geaz/simplyKeeb-60K/printedmx/keeb/positions.scad

withTrrs = true;

// [x, y]
screwPositions = [
    [5.2,-105.5],
    [22.6,-79.9],
    [60.7,-79.9],
    [98.8,-79.9],
    [98.8,-22.3],  
    [22.6,-22.3],  
    [60.7,-41.5]
];

bendPreventions = [
    [61, -22.3],
    [32, -41.5],
    [89, -41.5],
    [32, -60.5],
    [89, -60.5],
    [61, -79.9],
];

// x, y, rotation
proMicroPosition = [40,-36.2,0];
trrsPosition = [-12,-95.7,15];
