geaz/simplyKeeb-60K/pcb/RP2040_for_keebs.kicad_sch

## KiCad design pcb/RP2040_for_keebs.kicad_sch (2022-11-28)

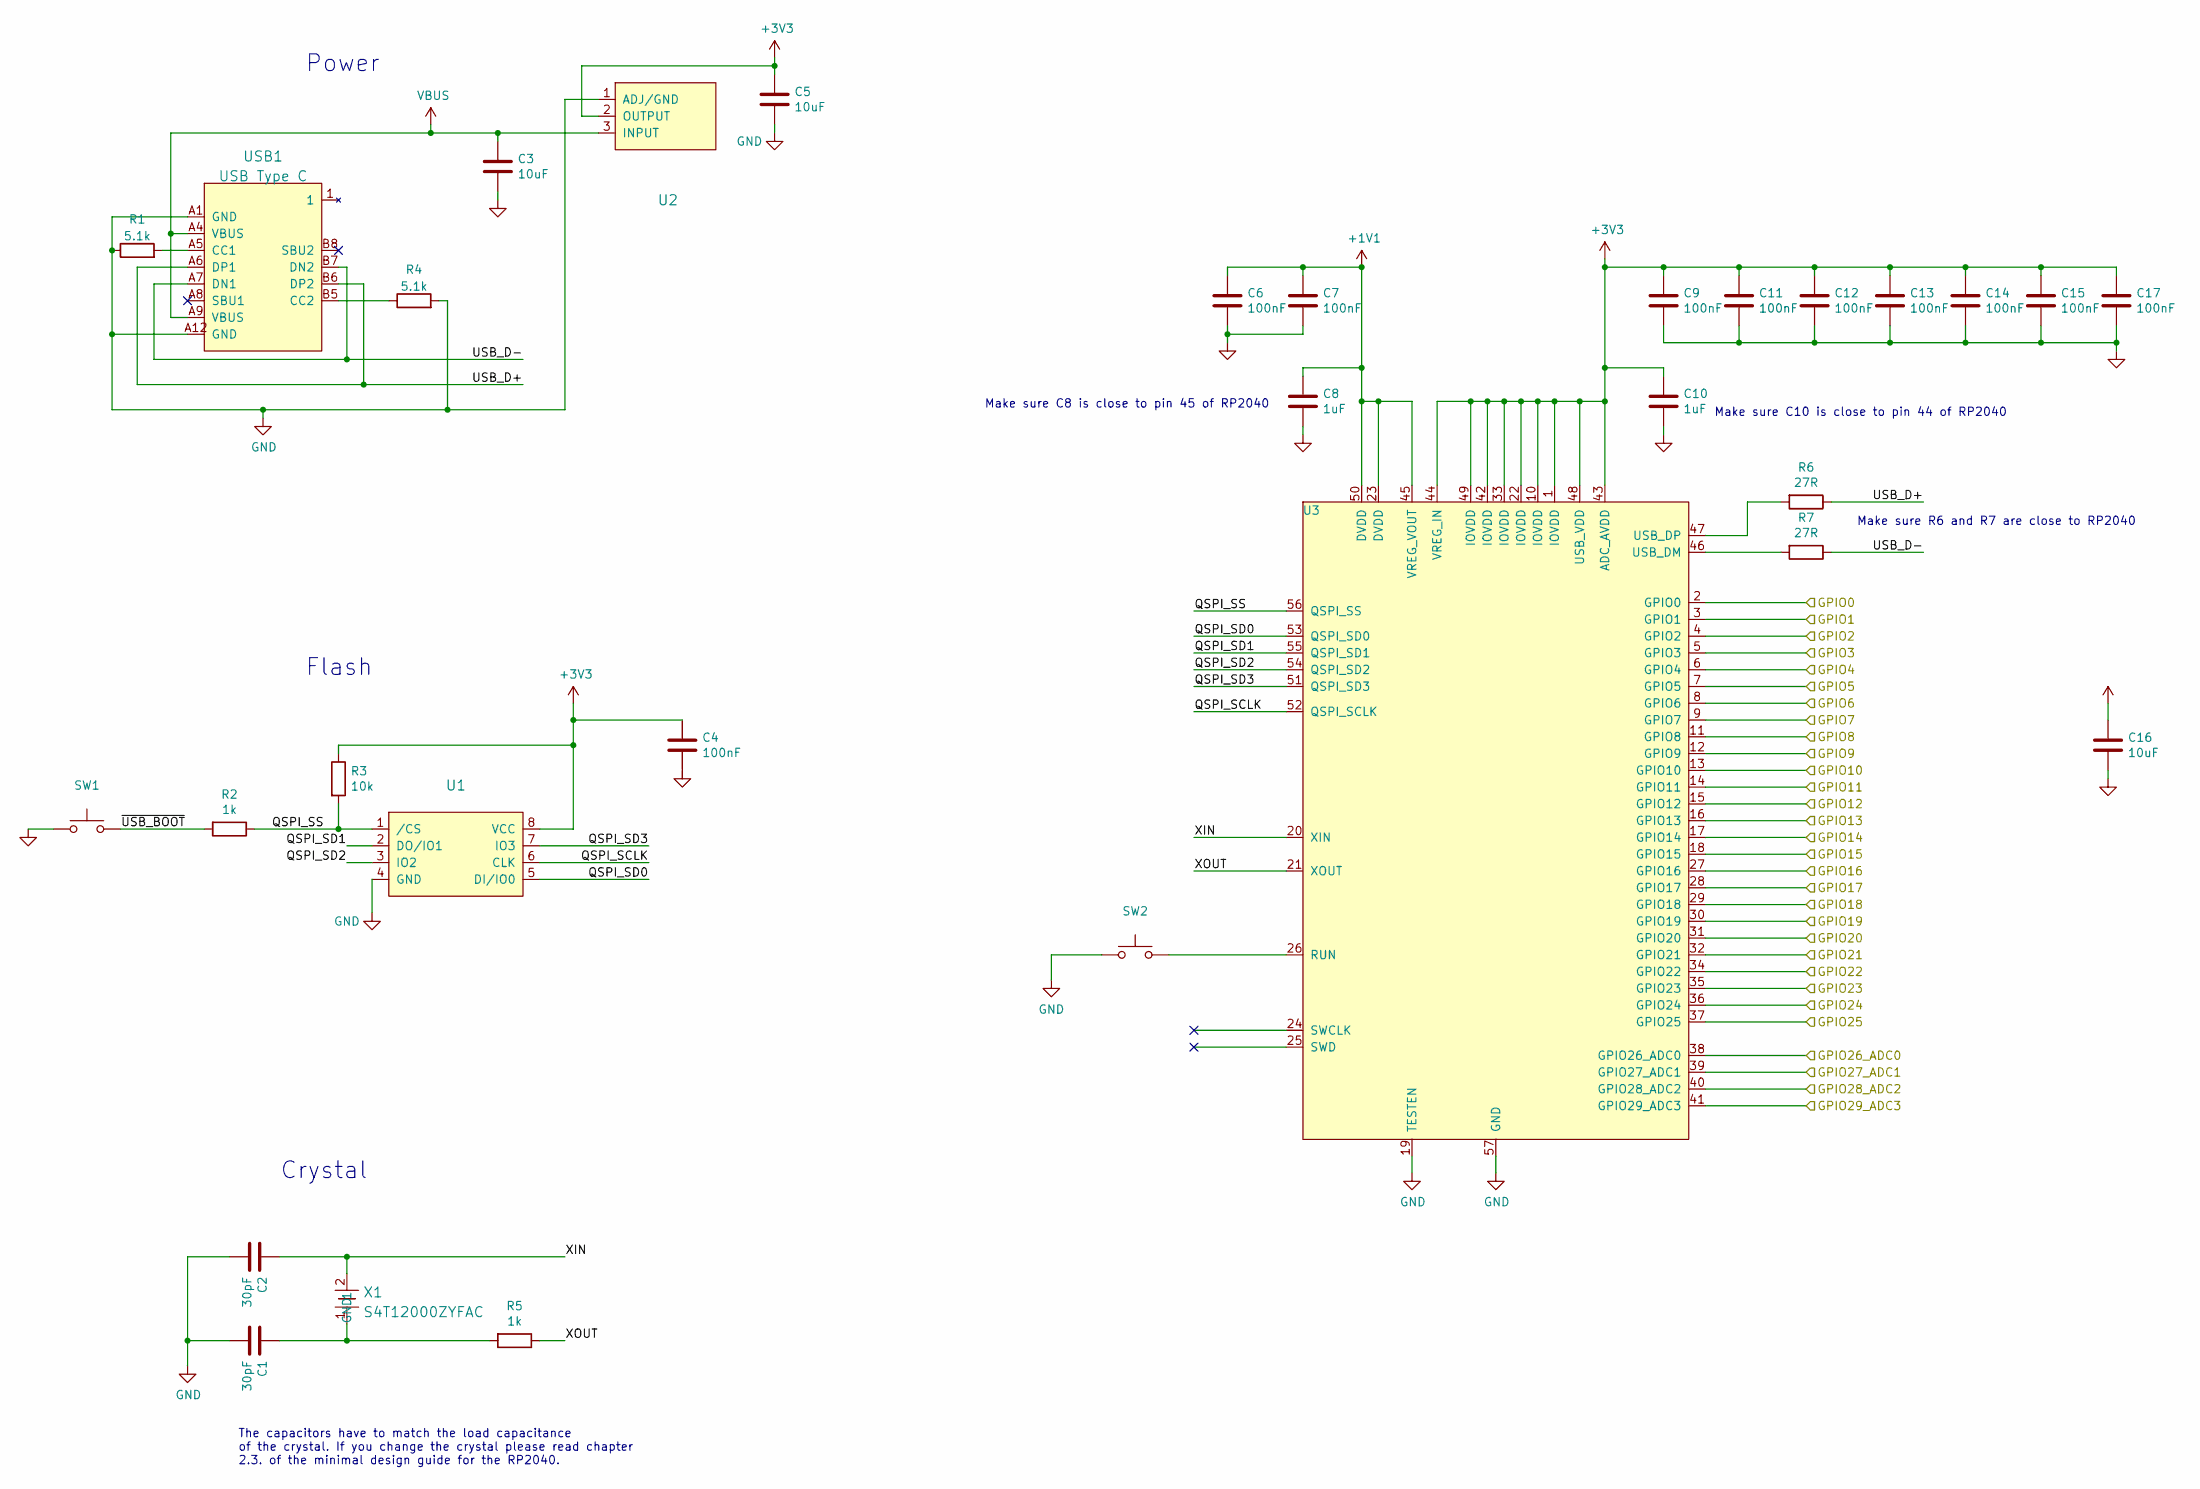
[picture p35: schematic RP2040_for_keebs.kicad_sch]

Parts:
C1, C2: 30pF; C_0402_1005Metric
C3, C5, C16: 10uF; C_0402_1005Metric
C4: 100nF; C_0402_1005Metric
C6, C7, C9, C11, C12, C13, C14, C15, C17: 100nF; C_0402_1005Metric; LCSC C83056
C8, C10: 1uF; C_0402_1005Metric; LCSC C92755
R1, R4: 5.1k; R_0402_1005Metric
R2, R5: 1k; R_0402_1005Metric
R3: 10k; R_0402_1005Metric
R6, R7: 27R; R_0402_1005Metric; LCSC C25100
SW1, SW2: SW-SMD_L6.0-W3.3-LS8.0
U1: SOIC-8_L5.3-W5.3-P1.27-LS8.0-BL; LCSC C82317
U2: SOT-223-3_L6.5-W3.4-P2.30-LS7.0-BR; LCSC C26537
U3: RP2040; LCSC C2040
USB1: USB Type C; USB-C-SMD_TYPE-C-31-M-31; LCSC C2760486
X1: S4T12000ZYFAC; CRYSTAL-SMD_L7.4-W4.0-LS8.0; LCSC C2149004

Connections:
+1V1: C6.1, C7.1, C8.1, U3.23 (DVDD), U3.45 (VREG_VOUT), U3.50 (DVDD)
+3V3: C4.1, C5.1, C9.1, C10.1, C11.1, C12.1, C13.1, C14.1, C15.1, C17.1, R3.1, U1.8 (VCC), U2.2 (OUTPUT), U3.1 (IOVDD), U3.10 (IOVDD), U3.22 (IOVDD), U3.33 (IOVDD), U3.42 (IOVDD), U3.43 (ADC_AVDD), U3.44 (VREG_IN), U3.48 (USB_VDD), U3.49 (IOVDD)
GND: C1.2, C2.2, C5.2, R1.1, R4.2, SW2.1, U1.4 (GND), U2.1 (ADJ/GND), U3.19 (TESTEN), U3.57 (GND), USB1.A1 (GND), USB1.A12 (GND)
GPIO0: U3.2 (GPIO0)
GPIO1: U3.3 (GPIO1)
GPIO2: U3.4 (GPIO2)
GPIO3: U3.5 (GPIO3)
GPIO4: U3.6 (GPIO4)
GPIO5: U3.7 (GPIO5)
GPIO6: U3.8 (GPIO6)
GPIO7: U3.9 (GPIO7)
GPIO8: U3.11 (GPIO8)
GPIO9: U3.12 (GPIO9)
GPIO10: U3.13 (GPIO10)
GPIO11: U3.14 (GPIO11)
GPIO12: U3.15 (GPIO12)
GPIO13: U3.16 (GPIO13)
GPIO14: U3.17 (GPIO14)
GPIO15: U3.18 (GPIO15)
GPIO16: U3.27 (GPIO16)
GPIO17: U3.28 (GPIO17)
GPIO18: U3.29 (GPIO18)
GPIO19: U3.30 (GPIO19)
GPIO20: U3.31 (GPIO20)
GPIO21: U3.32 (GPIO21)
GPIO22: U3.34 (GPIO22)
GPIO23: U3.35 (GPIO23)
GPIO24: U3.36 (GPIO24)
GPIO25: U3.37 (GPIO25)
GPIO26_ADC0: U3.38 (GPIO26_ADC0)
GPIO27_ADC1: U3.39 (GPIO27_ADC1)
GPIO28_ADC2: U3.40 (GPIO28_ADC2)
GPIO29_ADC3: U3.41 (GPIO29_ADC3)
unnamed: C1.1, R5.2, X1.1
unnamed: R1.2, USB1.A5 (CC1)
unnamed: R4.1, USB1.B5 (CC2)
unnamed: R6.2, U3.47 (USB_DP)
unnamed: R7.2, U3.46 (USB_DM)
unnamed: SW2.2, U3.26 (RUN)
QSPI_SCLK: U1.6 (CLK), U3.52 (QSPI_SCLK)
QSPI_SD0: U1.5 (DI/IO0), U3.53 (QSPI_SD0)
QSPI_SD1: U1.2 (DO/IO1), U3.55 (QSPI_SD1)
QSPI_SD2: U1.3 (IO2), U3.54 (QSPI_SD2)
QSPI_SD3: U1.7 (IO3), U3.51 (QSPI_SD3)
QSPI_SS: R2.1, R3.2, U1.1 (/CS), U3.56 (QSPI_SS)
USB_D+: R6.1, USB1.A6 (DP1), USB1.B6 (DP2)
USB_D-: R7.1, USB1.A7 (DN1), USB1.B7 (DN2)
VBUS: C3.1, U2.3 (INPUT), USB1.A4 (VBUS), USB1.A9 (VBUS)
XIN: C2.1, U3.20 (XIN), X1.2 (GND)
XOUT: R5.1, U3.21 (XOUT)
~: C3.2, C4.2, C6.2, C7.2, C8.2, C9.2, C10.2, C11.2, C12.2, C13.2, C14.2, C15.2, C16.1, C16.2, C17.2, SW1.1
~USB_BOOT: R2.2, SW1.2

Notes on the sheet:
Make sure C10 is close to pin 44 of RP2040
The capacitors have to match the load capacitance of the crystal. If you change the crystal please read chapter 2.3. of the minimal design guide for the RP2040.
Power
Crystal
Make sure C8 is close to pin 45 of RP2040
Flash
Make sure R6 and R7 are close to RP2040
