geaz/simplyKeeb-60K/pcb/simplyKeeb-60K.kicad_sch

## KiCad design pcb/simplyKeeb-60K.kicad_sch (2022-11-28)

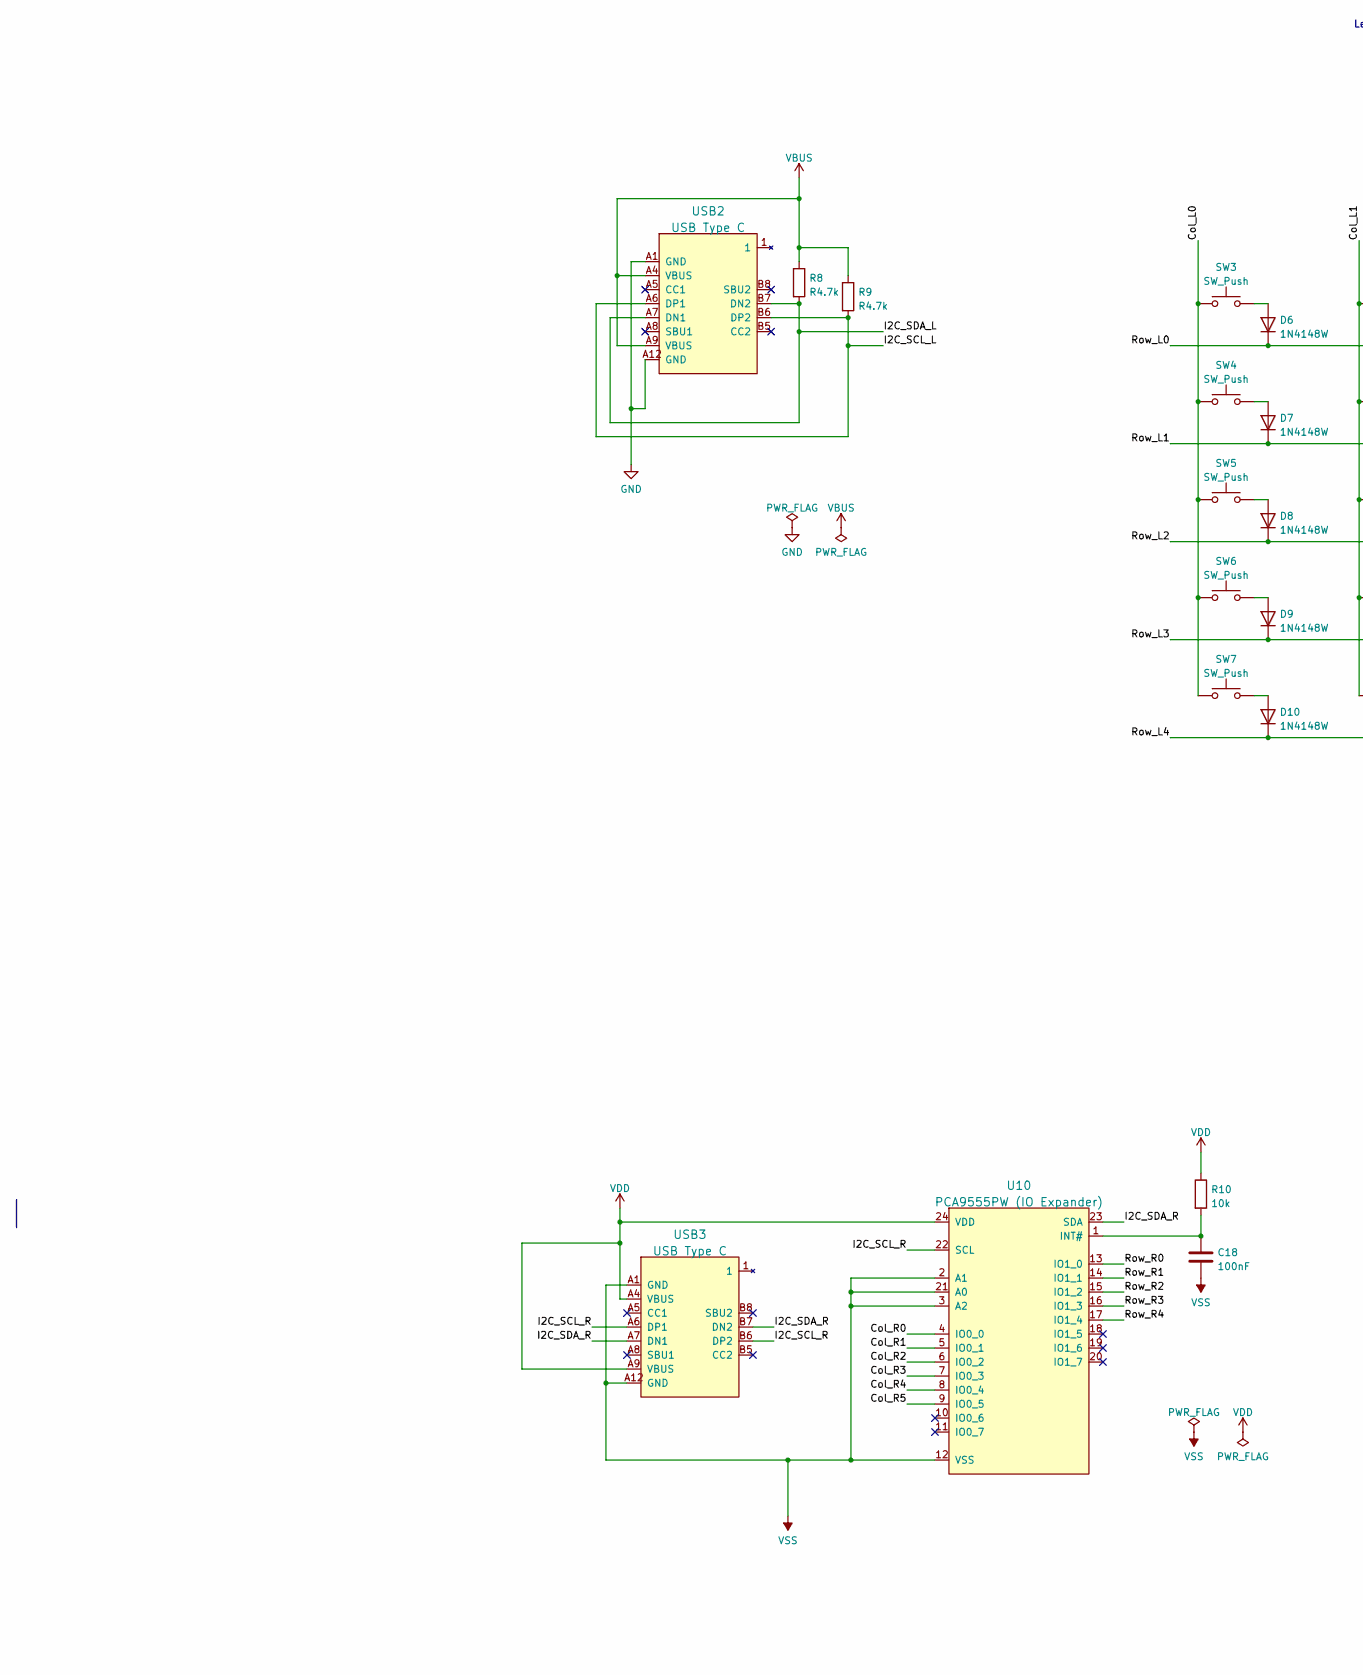
[picture p36: schematic simplyKeeb-60K.kicad_sch, part in row 1, column 1]

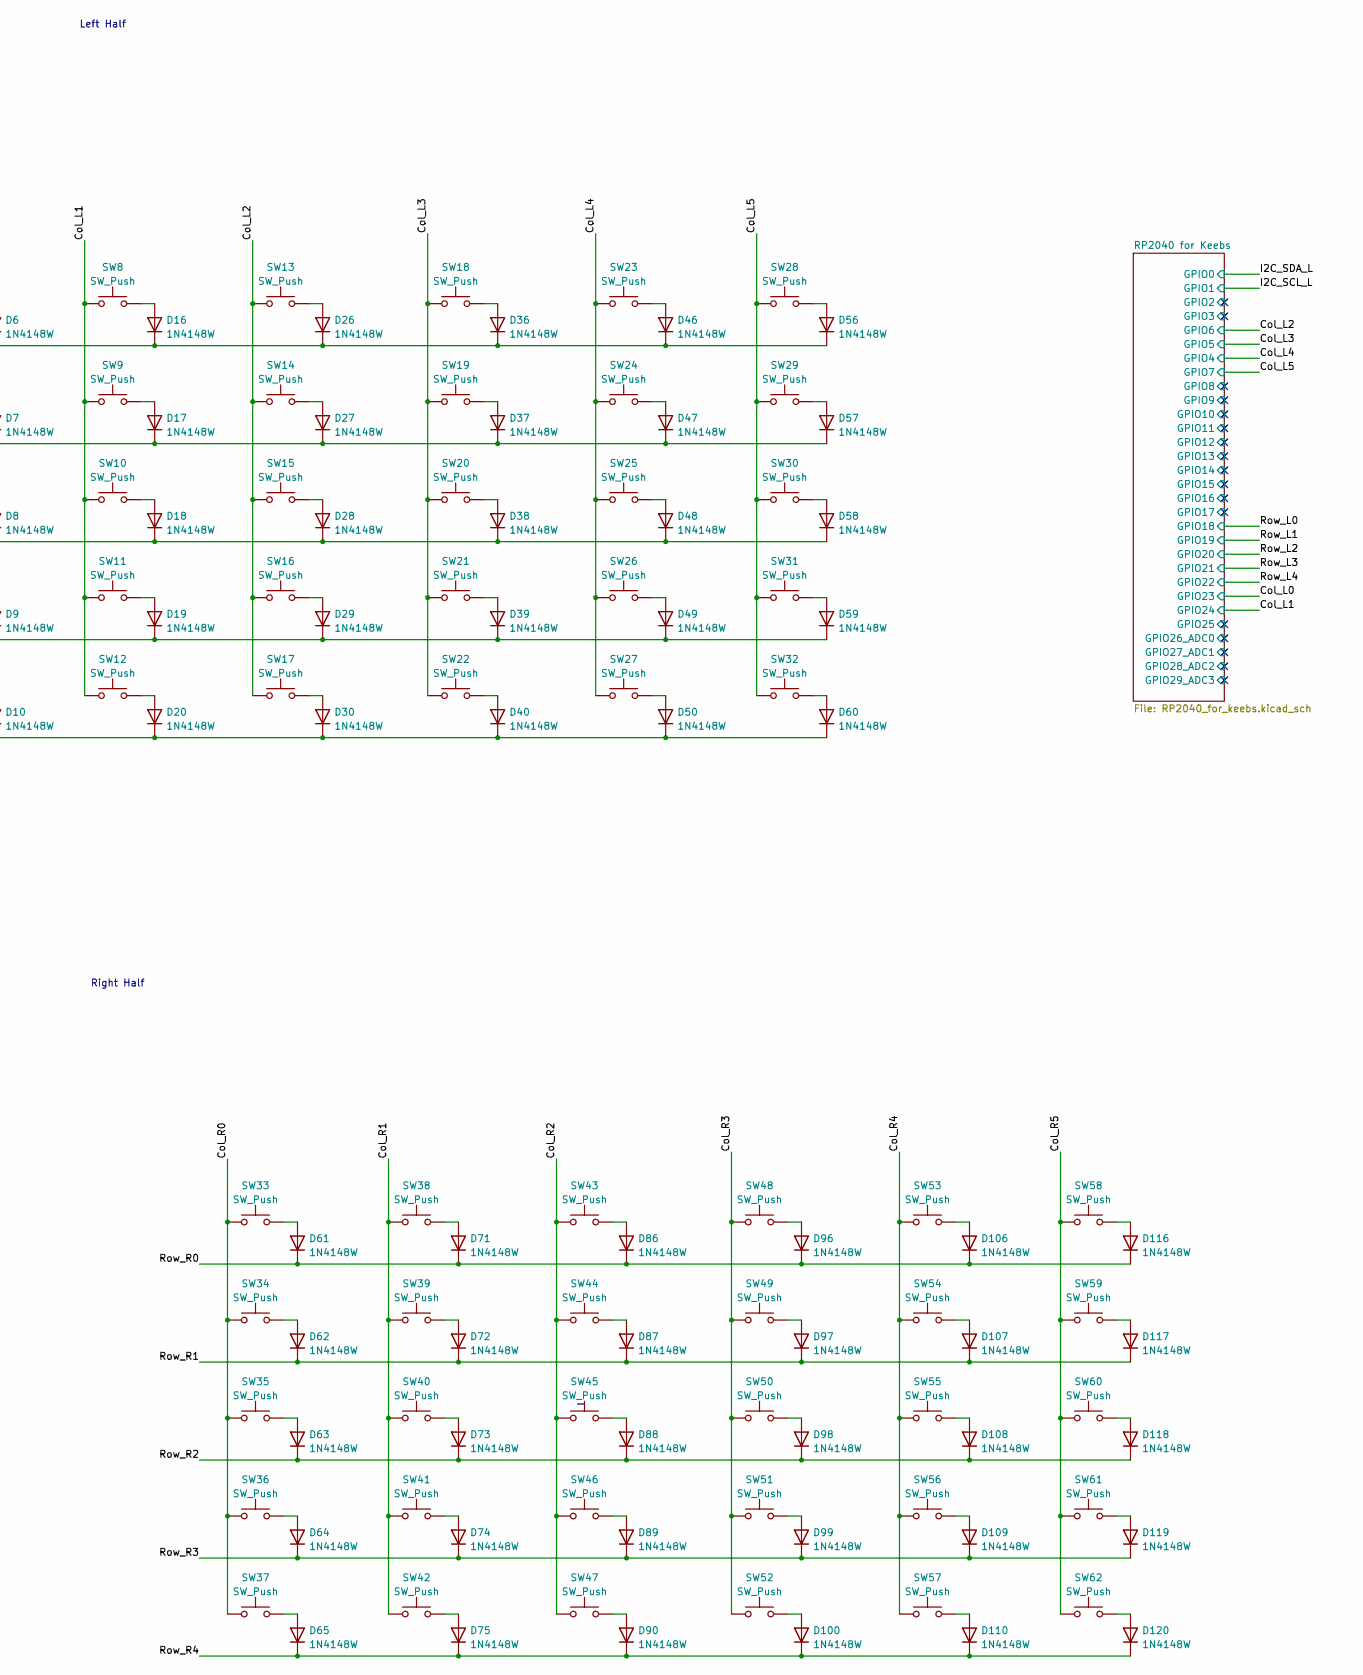
[picture p37: schematic simplyKeeb-60K.kicad_sch, part in row 1, column 2]

Parts:
C18: 100nF; C_0402_1005Metric
D6, D7, D8, D9, D10, D16, D17, D18, D19, D20, D26, D27, D28, D29, D30, D36, D37, D38, D39, D40, D46, D47, D48, D49, D50, D56, D57, D58, D59, D60, D61, D62, D63, D64, D65, D71, D72, D73, D74, D75, D86, D87, D88, D89, D90, D96, D97, D98, D99, D100, D106, D107, D108, D109, D110, D116, D117, D118, D119, D120: 1N4148W; D_SOD-123
R8, R9: R4.7k; R_0402_1005Metric
R10: 10k; R_0402_1005Metric
SW3, SW4, SW5, SW6, SW7, SW8, SW9, SW10, SW11, SW12, SW13, SW14, SW15, SW16, SW17, SW18, SW19, SW20, SW21, SW22, SW23, SW24, SW25, SW26, SW28, SW29, SW30, SW31, SW33, SW34, SW35, SW36, SW38, SW39, SW40, SW41, SW43, SW44, SW45, SW46, SW47, SW48, SW49, SW50, SW51, SW52, SW53, SW54, SW55, SW56, SW57, SW58, SW59, SW60, SW61, SW62: SW_Push; MXOnly-1U-Hotswap
SW27, SW42: SW_Push; MXOnly-1.5U-Hotswap-Vertical
SW32, SW37: SW_Push; MXOnly-2U-Hotswap-Vertical
U10: PCA9555PW (IO Expander); TSSOP-24_L7.8-W4.4-P0.65-LS6.4-BL; LCSC C128392
USB2, USB3: USB Type C; USB-C-SMD_TYPE-C-31-M-31; LCSC C2760486

Connections:
Col_L0: SW3.1, SW4.1, SW5.1, SW6.1, SW7.1
Col_L1: SW8.1, SW9.1, SW10.1, SW11.1, SW12.1
Col_L2: SW13.1, SW14.1, SW15.1, SW16.1, SW17.1
Col_L3: SW18.1, SW19.1, SW20.1, SW21.1, SW22.1
Col_L4: SW23.1, SW24.1, SW25.1, SW26.1, SW27.1
Col_L5: SW28.1, SW29.1, SW30.1, SW31.1, SW32.1
Col_R0: SW33.1, SW34.1, SW35.1, SW36.1, SW37.1, U10.4 (IO0_0)
Col_R1: SW38.1, SW39.1, SW40.1, SW41.1, SW42.1, U10.5 (IO0_1)
Col_R2: SW43.1, SW44.1, SW45.1, SW46.1, SW47.1, U10.6 (IO0_2)
Col_R3: SW48.1, SW49.1, SW50.1, SW51.1, SW52.1, U10.7 (IO0_3)
Col_R4: SW53.1, SW54.1, SW55.1, SW56.1, SW57.1, U10.8 (IO0_4)
Col_R5: SW58.1, SW59.1, SW60.1, SW61.1, SW62.1, U10.9 (IO0_5)
GND: USB2.A1 (GND), USB2.A12 (GND)
I2C_SCL_L: R9.2, USB2.A6 (DP1), USB2.B6 (DP2)
I2C_SCL_R: U10.22 (SCL), USB3.A6 (DP1), USB3.B6 (DP2)
I2C_SDA_L: R8.2, USB2.A7 (DN1), USB2.B7 (DN2)
I2C_SDA_R: U10.23 (SDA), USB3.A7 (DN1), USB3.B7 (DN2)
unnamed: C18.1, R10.2, U10.1 (INT#)
unnamed: D6.2 (A), SW3.2
unnamed: D7.2 (A), SW4.2
unnamed: D8.2 (A), SW5.2
unnamed: D9.2 (A), SW6.2
unnamed: D10.2 (A), SW7.2
unnamed: D16.2 (A), SW8.2
unnamed: D17.2 (A), SW9.2
unnamed: D18.2 (A), SW10.2
unnamed: D19.2 (A), SW11.2
unnamed: D20.2 (A), SW12.2
unnamed: D26.2 (A), SW13.2
unnamed: D27.2 (A), SW14.2
unnamed: D28.2 (A), SW15.2
unnamed: D29.2 (A), SW16.2
unnamed: D30.2 (A), SW17.2
unnamed: D36.2 (A), SW18.2
unnamed: D37.2 (A), SW19.2
unnamed: D38.2 (A), SW20.2
unnamed: D39.2 (A), SW21.2
unnamed: D40.2 (A), SW22.2
unnamed: D46.2 (A), SW23.2
unnamed: D47.2 (A), SW24.2
unnamed: D48.2 (A), SW25.2
unnamed: D49.2 (A), SW26.2
unnamed: D50.2 (A), SW27.2
unnamed: D56.2 (A), SW28.2
unnamed: D57.2 (A), SW29.2
unnamed: D58.2 (A), SW30.2
unnamed: D59.2 (A), SW31.2
unnamed: D60.2 (A), SW32.2
unnamed: D61.2 (A), SW33.2
unnamed: D62.2 (A), SW34.2
unnamed: D63.2 (A), SW35.2
unnamed: D64.2 (A), SW36.2
unnamed: D65.2 (A), SW37.2
unnamed: D71.2 (A), SW38.2
unnamed: D72.2 (A), SW39.2
unnamed: D73.2 (A), SW40.2
unnamed: D74.2 (A), SW41.2
unnamed: D75.2 (A), SW42.2
unnamed: D86.2 (A), SW43.2
unnamed: D87.2 (A), SW44.2
unnamed: D88.2 (A), SW45.2
unnamed: D89.2 (A), SW46.2
unnamed: D90.2 (A), SW47.2
unnamed: D96.2 (A), SW48.2
unnamed: D97.2 (A), SW49.2
unnamed: D98.2 (A), SW50.2
unnamed: D99.2 (A), SW51.2
unnamed: D100.2 (A), SW52.2
unnamed: D106.2 (A), SW53.2
unnamed: D107.2 (A), SW54.2
unnamed: D108.2 (A), SW55.2
unnamed: D109.2 (A), SW56.2
unnamed: D110.2 (A), SW57.2
unnamed: D116.2 (A), SW58.2
unnamed: D117.2 (A), SW59.2
unnamed: D118.2 (A), SW60.2
unnamed: D119.2 (A), SW61.2
unnamed: D120.2 (A), SW62.2
Row_L0: D6.1 (K), D16.1 (K), D26.1 (K), D36.1 (K), D46.1 (K), D56.1 (K)
Row_L1: D7.1 (K), D17.1 (K), D27.1 (K), D37.1 (K), D47.1 (K), D57.1 (K)
Row_L2: D8.1 (K), D18.1 (K), D28.1 (K), D38.1 (K), D48.1 (K), D58.1 (K)
Row_L3: D9.1 (K), D19.1 (K), D29.1 (K), D39.1 (K), D49.1 (K), D59.1 (K)
Row_L4: D10.1 (K), D20.1 (K), D30.1 (K), D40.1 (K), D50.1 (K), D60.1 (K)
Row_R0: D61.1 (K), D71.1 (K), D86.1 (K), D96.1 (K), D106.1 (K), D116.1 (K), U10.13 (IO1_0)
Row_R1: D62.1 (K), D72.1 (K), D87.1 (K), D97.1 (K), D107.1 (K), D117.1 (K), U10.14 (IO1_1)
Row_R2: D63.1 (K), D73.1 (K), D88.1 (K), D98.1 (K), D108.1 (K), D118.1 (K), U10.15 (IO1_2)
Row_R3: D64.1 (K), D74.1 (K), D89.1 (K), D99.1 (K), D109.1 (K), D119.1 (K), U10.16 (IO1_3)
Row_R4: D65.1 (K), D75.1 (K), D90.1 (K), D100.1 (K), D110.1 (K), D120.1 (K), U10.17 (IO1_4)
VBUS: R8.1, R9.1, USB2.A4 (VBUS), USB2.A9 (VBUS)
VDD: R10.1, U10.24 (VDD), USB3.A4 (VBUS), USB3.A9 (VBUS)
VSS: C18.2, U10.2 (A1), U10.3 (A2), U10.12 (VSS), U10.21 (A0), USB3.A1 (GND), USB3.A12 (GND)

Notes on the sheet:
Right Half
Left Half
